orlopau/coffee-scale/code/fonts/roboto/regular_10.png

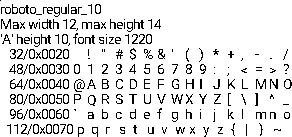
code/fonts/roboto/regular_10.png
