orlopau/coffee-scale/code/fonts/roboto/regular_20.png

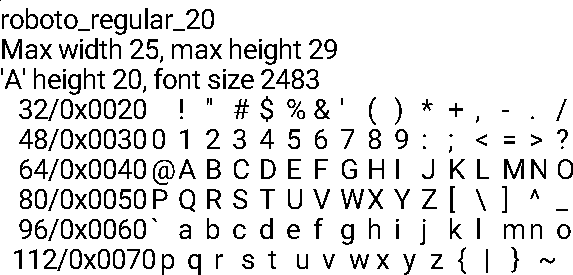
code/fonts/roboto/regular_20.png
