orlopau/coffee-scale/code/fonts/roboto_mono/regular_10.png

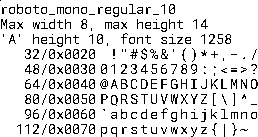
code/fonts/roboto_mono/regular_10.png
