orlopau/coffee-scale/code/fonts/roboto_mono/regular_20.png

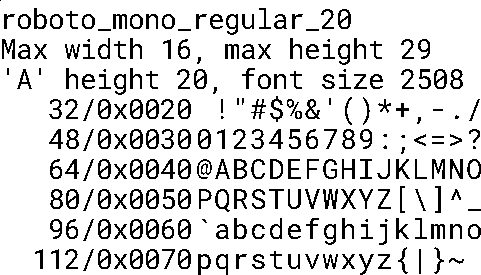
code/fonts/roboto_mono/regular_20.png
