orlopau/coffee-scale/docs/img/pcb.png

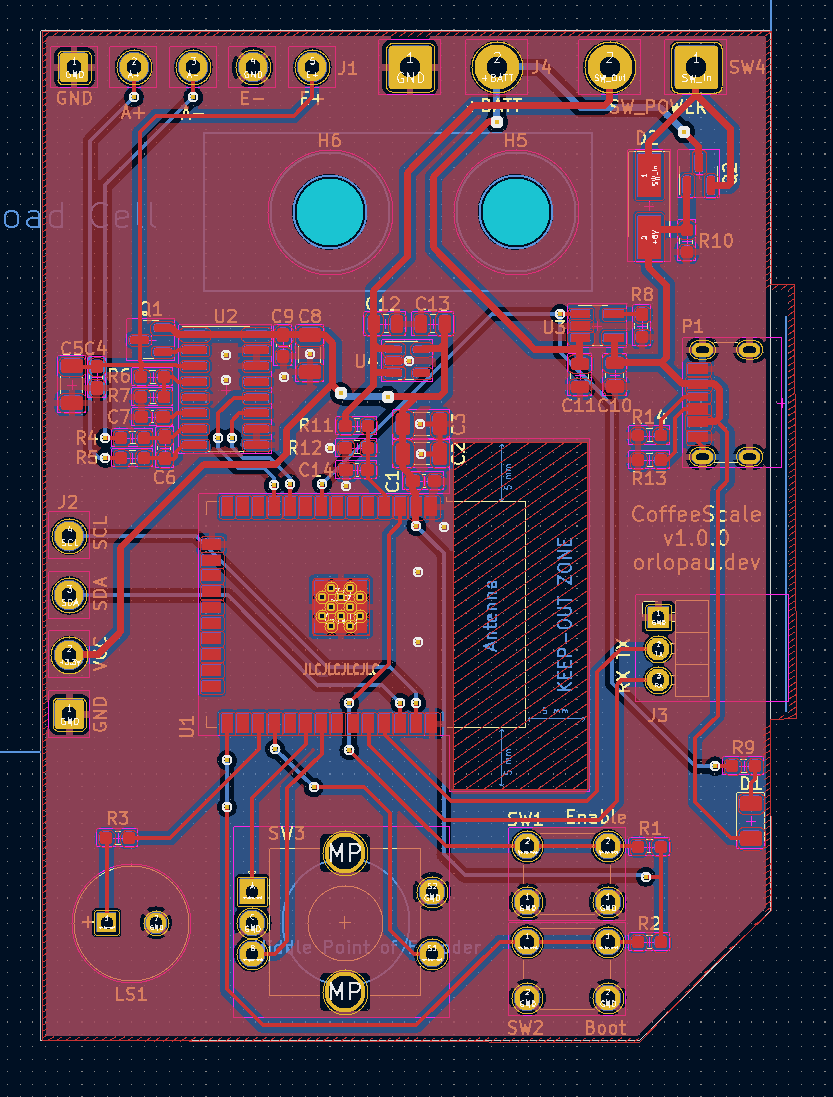
docs/img/pcb.png
