orlopau/coffee-scale/code/test/native/test_screenshots/screens/updater_wifi_setup.png

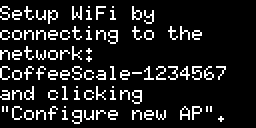
code/test/native/test_screenshots/screens/updater_wifi_setup.png
