orlopau/coffee-scale/code/test/native/test_screenshots/screens/calibration_add_weight.png

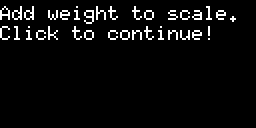
code/test/native/test_screenshots/screens/calibration_add_weight.png
