orlopau/coffee-scale/code/test/native/test_screenshots/screens/calibration_begin.png

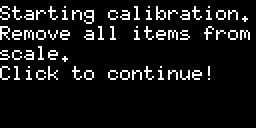
code/test/native/test_screenshots/screens/calibration_begin.png
