orlopau/coffee-scale/code/test/native/test_screenshots/screens/calibration_calibrating.png

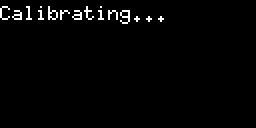
code/test/native/test_screenshots/screens/calibration_calibrating.png
