orlopau/coffee-scale/code/test/native/test_screenshots/screens/calibration_end.png

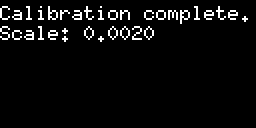
code/test/native/test_screenshots/screens/calibration_end.png
