orlopau/coffee-scale/code/test/native/test_screenshots/screens/espresso_brewing.png

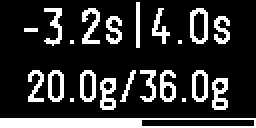
code/test/native/test_screenshots/screens/espresso_brewing.png
