orlopau/coffee-scale/code/test/native/test_screenshots/screens/espresso_idle.png

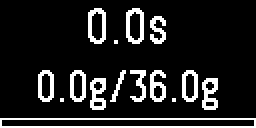
code/test/native/test_screenshots/screens/espresso_idle.png
