orlopau/coffee-scale/code/test/native/test_screenshots/screens/mode_switcher_1.png

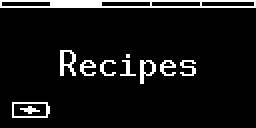
code/test/native/test_screenshots/screens/mode_switcher_1.png
