orlopau/coffee-scale/code/test/native/test_screenshots/screens/mode_switcher_3.png

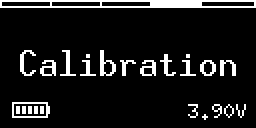
code/test/native/test_screenshots/screens/mode_switcher_3.png
