orlopau/coffee-scale/code/test/native/test_screenshots/screens/recipe_brewing_1_pour_1.png

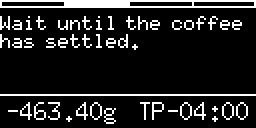
code/test/native/test_screenshots/screens/recipe_brewing_1_pour_1.png
