orlopau/coffee-scale/code/test/native/test_screenshots/screens/recipe_brewing_2_pour_2.png

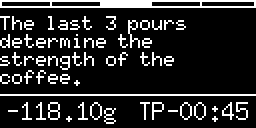
code/test/native/test_screenshots/screens/recipe_brewing_2_pour_2.png
