orlopau/coffee-scale/code/test/native/test_screenshots/screens/recipe_brewing_3_pour_1.png

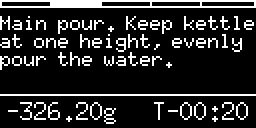
code/test/native/test_screenshots/screens/recipe_brewing_3_pour_1.png
