orlopau/coffee-scale/code/test/native/test_screenshots/screens/recipe_done.png

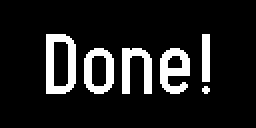
code/test/native/test_screenshots/screens/recipe_done.png
