orlopau/coffee-scale/code/test/native/test_screenshots/screens/recipe_prepare_empty.png

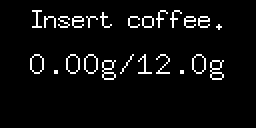
code/test/native/test_screenshots/screens/recipe_prepare_empty.png
