orlopau/coffee-scale/code/test/native/test_screenshots/screens/recipe_ratio_adjusted.png

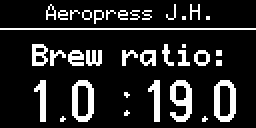
code/test/native/test_screenshots/screens/recipe_ratio_adjusted.png
