orlopau/coffee-scale/code/test/native/test_screenshots/screens/recipe_summary_0.png

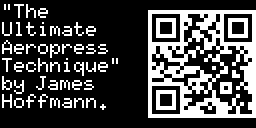
code/test/native/test_screenshots/screens/recipe_summary_0.png
