orlopau/coffee-scale/code/test/native/test_screenshots/screens/recipe_summary_2.png

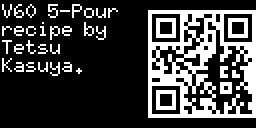
code/test/native/test_screenshots/screens/recipe_summary_2.png
