orlopau/coffee-scale/code/test/native/test_screenshots/screens/recipe_switcher_first.png

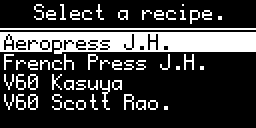
code/test/native/test_screenshots/screens/recipe_switcher_first.png
