orlopau/coffee-scale/code/test/native/test_screenshots/screens/recipe_switcher_last.png

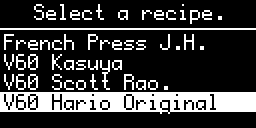
code/test/native/test_screenshots/screens/recipe_switcher_last.png
