orlopau/coffee-scale/code/test/native/test_screenshots/screens/recipe_weight_adjusted_down.png

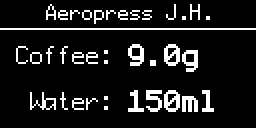
code/test/native/test_screenshots/screens/recipe_weight_adjusted_down.png
