orlopau/coffee-scale/code/test/native/test_screenshots/screens/recipe_weight_adjusted_up.png

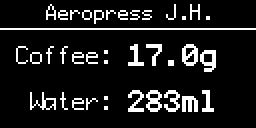
code/test/native/test_screenshots/screens/recipe_weight_adjusted_up.png
