orlopau/coffee-scale/code/test/native/test_screenshots/screens/recipe_weight_default_off.png

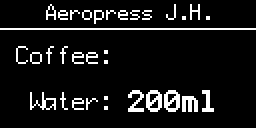
code/test/native/test_screenshots/screens/recipe_weight_default_off.png
