orlopau/coffee-scale/code/test/native/test_screenshots/screens/scale_negative.png

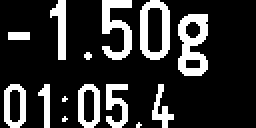
code/test/native/test_screenshots/screens/scale_negative.png
