orlopau/coffee-scale/code/test/native/test_screenshots/screens/scale_running.png

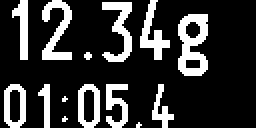
code/test/native/test_screenshots/screens/scale_running.png
