orlopau/coffee-scale/code/test/native/test_screenshots/screens/scale_zero.png

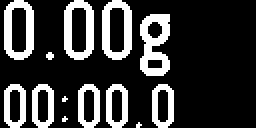
code/test/native/test_screenshots/screens/scale_zero.png
