orlopau/coffee-scale/code/test/native/test_screenshots/screens/settings_first.png

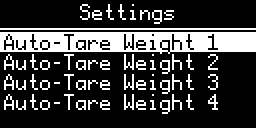
code/test/native/test_screenshots/screens/settings_first.png
