orlopau/coffee-scale/code/test/native/test_screenshots/screens/settings_middle.png

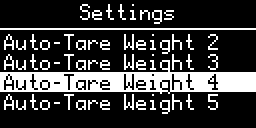
code/test/native/test_screenshots/screens/settings_middle.png
