orlopau/coffee-scale/code/test/native/test_screenshots/screens/settings_value_down.png

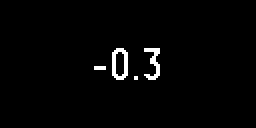
code/test/native/test_screenshots/screens/settings_value_down.png
