orlopau/coffee-scale/code/test/native/test_screenshots/screens/updater_dev_not_found.png

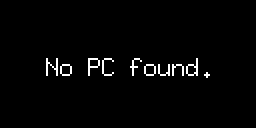
code/test/native/test_screenshots/screens/updater_dev_not_found.png
