orlopau/coffee-scale/code/test/native/test_screenshots/screens/updater_dev_searching.png

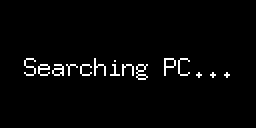
code/test/native/test_screenshots/screens/updater_dev_searching.png
