orlopau/coffee-scale/code/test/native/test_screenshots/screens/updater_failed.png

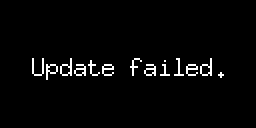
code/test/native/test_screenshots/screens/updater_failed.png
