orlopau/coffee-scale/code/test/native/test_screenshots/screens/updater_language_0.png

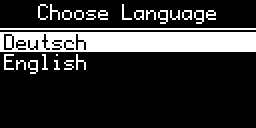
code/test/native/test_screenshots/screens/updater_language_0.png
