orlopau/coffee-scale/code/test/native/test_screenshots/screens/updater_language_1.png

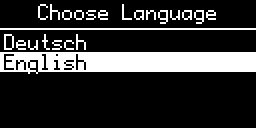
code/test/native/test_screenshots/screens/updater_language_1.png
