orlopau/coffee-scale/code/test/native/test_screenshots/screens/updater_no_update.png

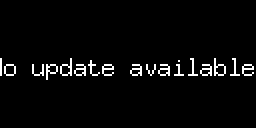
code/test/native/test_screenshots/screens/updater_no_update.png
