orlopau/coffee-scale/code/test/native/test_screenshots/screens/updater_progress.png

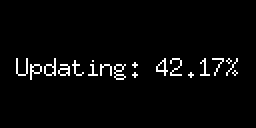
code/test/native/test_screenshots/screens/updater_progress.png
