orlopau/coffee-scale/code/test/native/test_screenshots/screens/updater_success.png

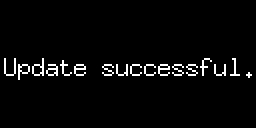
code/test/native/test_screenshots/screens/updater_success.png
