orlopau/coffee-scale/code/src/modes/mode_recipe.cpp

#include <cstring>

#include "mode_recipe.h"
#include "millis.h"
#include "data/localization.h"
#include "interface.h"

#include "modes/steps/step_switcher.h"
#include "modes/steps/step_summary.h"
#include "modes/steps/step_config_ratio.h"
#include "modes/steps/step_config_weight.h"
#include "modes/steps/step_prepare.h"
#include "modes/steps/step_brewing.h"
#include "modes/steps/step_done.h"

ModeRecipes::ModeRecipes(WeightSensor &weightSensor, const Recipe recipes[],
                         uint8_t recipeCount)
    : weightSensor(weightSensor), currentRecipeStep(0),
      recipeSteps{
          new RecipeSwitcherStep(recipeStepState, recipes, recipeCount),
          new RecipeSummaryStep(recipeStepState),
          new RecipeConfigRatioStep(recipeStepState),
          new RecipeConfigWeightStep(recipeStepState),
          new RecipePrepare(recipeStepState, weightSensor),
          new RecipeBrewing(recipeStepState, weightSensor),
          new RecipeDone(recipeStepState),
      } {};

void ModeRecipes::update()
{
    // update current step
    // checks if step is ready to advance, and if so, advances
    // if long click, go back to previous step
    // when all steos are done, advancing to next step returns to first step
    uint8_t previousStep = currentRecipeStep;
    if (Interface::getEncoderClick() == ClickType::SINGLE && recipeSteps[currentRecipeStep]->canStepForward())
    {
        currentRecipeStep++;
        if (currentRecipeStep >= recipeStepCount)
        {
            currentRecipeStep = 0;
        }
    }
    else if (Interface::getEncoderClick() == ClickType::LONG && recipeSteps[currentRecipeStep]->canStepBackward())
    {
        if (currentRecipeStep > 0)
        {
            currentRecipeStep--;
        }
    }

    if (previousStep != currentRecipeStep)
    {
        recipeSteps[previousStep]->exit();
        recipeSteps[currentRecipeStep]->enter();
        Interface::consumeEncoderClick();
    }

    recipeSteps[currentRecipeStep]->update();
}

void ModeRecipes::render(Canvas &canvas) { recipeSteps[currentRecipeStep]->render(canvas); }

bool ModeRecipes::canSwitchMode()
{
    return currentRecipeStep == 0;
}

uint8_t ModeRecipes::getCurrentStepIndex()
{
    return currentRecipeStep;
}

const char *ModeRecipes::getName()
{
    return MODE_NAME_RECIPES;
}
