orlopau/coffee-scale/code/src/modes/mode_recipe.h

#pragma once

#include "mode.h"
#include "recipe.h"
#include "modes/steps/step.h"
#include "weight_sensor.h"

class ModeRecipes : public Mode
{
public:
    ModeRecipes(WeightSensor &weightSensor, const Recipe recipes[], uint8_t recipeCount);
    void update() override;
    void render(Canvas &canvas) override;
    const char *getName();
    bool canSwitchMode();
    uint8_t getCurrentStepIndex();

private:
    WeightSensor &weightSensor;

    RecipeStepState recipeStepState;

    uint8_t currentRecipeStep;
    static const uint8_t recipeStepCount = 7;
    RecipeStep *recipeSteps[recipeStepCount];
};
