orlopau/coffee-scale/code/src/modes/steps/step_prepare.h

#pragma once

#include "step.h"
#include "weight_sensor.h"

class RecipePrepare : public RecipeStep
{
public:
    RecipePrepare(RecipeStepState &state, WeightSensor &weightSensor);
    void update() override;
    void render(Canvas &canvas) override;
    void enter() override;
    void exit() override;
private:
    RecipeStepState &state;
    WeightSensor &weightSensor;
};
