orlopau/coffee-scale/code/src/modes/steps/step_summary.h

#pragma once

#include "step.h"

class RecipeSummaryStep : public RecipeStep
{
public:
    RecipeSummaryStep(RecipeStepState &state);
    void update() override {}
    void render(Canvas &canvas) override;

private:
    RecipeStepState &state;
};
