orlopau/coffee-scale/code/src/modes/steps/step_switcher.cpp

#include "step_switcher.h"
#include "data/localization.h"
#include "interface.h"
#include "ui/widgets.h"

RecipeSwitcherStep::~RecipeSwitcherStep()
{
    delete[] recipeSwitcherEntries;
}

RecipeSwitcherStep::RecipeSwitcherStep(RecipeStepState &state, const Recipe recipes[], const uint8_t recipeCount)
    : state(state), recipes(recipes), recipeCount(recipeCount), recipeIndex(0)
{
    recipeSwitcherEntries = new const char *[recipeCount];
    for (uint8_t i = 0; i < recipeCount; i++)
    {
        recipeSwitcherEntries[i] = recipes[i].name;
    }
}

void RecipeSwitcherStep::update()
{
    int16_t change = static_cast<int16_t>(Interface::getEncoderDirection());

    if (recipeIndex + change >= recipeCount)
    {
        recipeIndex = recipeCount - 1;
    }
    else if (recipeIndex + change < 0)
    {
        recipeIndex = 0;
    }
    else
    {
        recipeIndex += change;
    }
}

void RecipeSwitcherStep::render(Canvas &canvas)
{
    Widgets::switcher(canvas, DISPLAY_RECIPE_SWITCHER_TITLE, recipeIndex, recipeCount, recipeSwitcherEntries);
}

void RecipeSwitcherStep::exit()
{
    state.originalRecipe = &recipes[recipeIndex];
    state.configRecipe = recipes[recipeIndex];
}
