orlopau/coffee-scale/code/src/modes/steps/step_switcher.h

#pragma once

#include "step.h"

class RecipeSwitcherStep : public RecipeStep
{
public:
    ~RecipeSwitcherStep();
    RecipeSwitcherStep(RecipeStepState &state, const Recipe recipes[],
                       const uint8_t recipeCount);
    void update() override;
    void render(Canvas &canvas) override;
    void exit() override;
    uint8_t recipeIndex;

private:
    RecipeStepState &state;

    const Recipe *recipes;
    const char **recipeSwitcherEntries;
    uint8_t recipeCount;
};
