orlopau/coffee-scale/code/src/data/bitmaps.h

#pragma once

#define chemex_width 40
#define chemex_height 64
static unsigned char chemex_bits[] = {
    0x00, 0x00, 0x00, 0x00, 0x00, 0xc0, 0xff, 0xff, 0xff, 0x03, 0xe0, 0xff,
    0xff, 0xff, 0x07, 0x60, 0x00, 0x00, 0x00, 0x06, 0xc0, 0x00, 0x00, 0x00,
    0x03, 0xc0, 0x00, 0x00, 0x00, 0x03, 0xc0, 0x01, 0x00, 0x80, 0x03, 0x80,
    0x01, 0x18, 0x80, 0x01, 0x80, 0x01, 0x18, 0x80, 0x01, 0x00, 0x03, 0x18,
    0xc0, 0x00, 0x00, 0x03, 0x3c, 0xc0, 0x00, 0x00, 0x07, 0x3c, 0x60, 0x00,
    0x00, 0x06, 0x3c, 0x60, 0x00, 0x00, 0x0e, 0x18, 0x70, 0x00, 0x00, 0x0c,
    0x00, 0x30, 0x00, 0x00, 0x0c, 0x00, 0x30, 0x00, 0x00, 0x18, 0x00, 0x18,
    0x00, 0x00, 0x18, 0x00, 0x18, 0x00, 0x00, 0x38, 0x00, 0x1c, 0x00, 0x00,
    0x30, 0x00, 0x0c, 0x00, 0x00, 0x30, 0x00, 0x0c, 0x00, 0x00, 0xf0, 0xff,
    0x0f, 0x00, 0x00, 0xf8, 0xff, 0x1f, 0x00, 0x00, 0x18, 0x00, 0x18, 0x00,
    0x00, 0x18, 0x00, 0x18, 0x00, 0x00, 0x18, 0x00, 0x18, 0x00, 0x00, 0x18,
    0x00, 0x18, 0x00, 0x00, 0x18, 0x00, 0x18, 0x00, 0x00, 0x18, 0x00, 0x18,
    0x00, 0x00, 0x18, 0x00, 0x18, 0x00, 0x00, 0x18, 0x00, 0x18, 0x00, 0x00,
    0x18, 0x00, 0x18, 0x00, 0x00, 0xf8, 0xff, 0x1f, 0x00, 0x00, 0xf0, 0xff,
    0x0f, 0x00, 0x00, 0x30, 0x00, 0x0c, 0x00, 0x00, 0x30, 0x00, 0x0c, 0x00,
    0x00, 0x18, 0x00, 0x18, 0x00, 0x00, 0x18, 0x00, 0x18, 0x00, 0x00, 0x0c,
    0x00, 0x38, 0x00, 0x00, 0x0c, 0x00, 0x30, 0x00, 0x00, 0x0e, 0x00, 0x70,
    0x00, 0x00, 0x06, 0x00, 0x60, 0x00, 0x00, 0x07, 0x00, 0xe0, 0x00, 0x00,
    0x03, 0x00, 0xc0, 0x00, 0x80, 0x03, 0x00, 0xc0, 0x01, 0x80, 0x01, 0x00,
    0x80, 0x01, 0xc0, 0x01, 0x00, 0x80, 0x03, 0xc0, 0xfc, 0xff, 0x1f, 0x03,
    0xe0, 0xfc, 0xff, 0x3f, 0x07, 0x60, 0xfe, 0xff, 0x3f, 0x06, 0x60, 0xfe,
    0xff, 0x7f, 0x06, 0x30, 0xff, 0xff, 0x7f, 0x0c, 0x30, 0xff, 0xff, 0xff,
    0x0c, 0x18, 0xff, 0xff, 0xff, 0x18, 0x98, 0xff, 0xff, 0xff, 0x39, 0x8c,
    0xff, 0xff, 0xff, 0x31, 0xcc, 0xff, 0xff, 0xff, 0x33, 0xc6, 0xff, 0xff,
    0xff, 0x63, 0xc6, 0xff, 0xff, 0xff, 0x63, 0x06, 0x00, 0x00, 0x00, 0x60,
    0x0e, 0x00, 0x00, 0x00, 0x70, 0xfc, 0xff, 0xff, 0xff, 0x3f, 0xf8, 0xff,
    0xff, 0xff, 0x1f, 0x00, 0x00, 0x00, 0x00, 0x00};
