orlopau/coffee-scale/code/test/native/test_mode_default/main.cpp

#include <unity.h>
#include "mode.h"
#include "mocks.h"
#include "stopwatch.h"

#include <chrono>
#include <thread>

static Stopwatch *stopwatch;
static MockWeightSensor *weightSensor;
static MockButtons *buttons;
static MockDisplay *display;

ModeDefault *modeDefault;

void setUp(void)
{
    stopwatch = new Stopwatch();
    weightSensor = new MockWeightSensor();
    buttons = new MockButtons();
    display = new MockDisplay();
    modeDefault = new ModeDefault(*weightSensor, *buttons, *display, *stopwatch);
}

void tearDown(void)
{
    delete stopwatch;
    delete buttons;
    delete display;
    delete modeDefault;
    delete weightSensor;
}

void test_stopwatch_start_when_click(void)
{
    TEST_ASSERT_FALSE(stopwatch->isRunning());
    buttons->encoderClick = ClickType::SINGLE;
    modeDefault->update();
    TEST_ASSERT_TRUE(stopwatch->isRunning());
}

void test_stopwatch_stop_when_click_again(void)
{
    buttons->encoderClick = ClickType::SINGLE;
    modeDefault->update();
    modeDefault->update();
    TEST_ASSERT_FALSE(stopwatch->isRunning());
}

void test_loadcell_tare_when_encoder_rotated(void)
{
    weightSensor->weight = 1;

    buttons->encoderDirection = EncoderDirection::CW;
    modeDefault->update();
    TEST_ASSERT_EQUAL(0, weightSensor->getWeight());
}

void test_display_shows_weight(void)
{
    weightSensor->weight = 1;

    modeDefault->update();
    TEST_ASSERT_EQUAL(1.0, display->weight);
}

void test_display_shows_time(void)
{
    stopwatch->start();
    std::this_thread::sleep_for(std::chrono::milliseconds(2));
    modeDefault->update();
    TEST_ASSERT_GREATER_OR_EQUAL(2, display->time);
}

int main(void)
{
    UNITY_BEGIN();
    RUN_TEST(test_stopwatch_start_when_click);
    RUN_TEST(test_stopwatch_stop_when_click_again);

    RUN_TEST(test_loadcell_tare_when_encoder_rotated);
    RUN_TEST(test_display_shows_weight);
    RUN_TEST(test_display_shows_time);
    UNITY_END();
}
