orlopau/coffee-scale/code/test/embedded/test_embedded/test_display.h

#include <unity.h>

#include "embedded/constants.h"
#include "embedded/u8g_display.h"
#include "confirm.h"

U8GDisplay display(PIN_I2C_SDA, PIN_I2C_SCL);

void test_display_text(void)
{
    display.begin();
    display.display(1, 1000);
    wait_confirm();
}

void test_display_all()
{
    RUN_TEST(test_display_text);
}
